uStepper/uStepperS/Examples/DropIn/DropIn.ino

/*
*			DropIn example sketch!
*
*		This sketch is all the software that is needed for adding closed loop position control 
*		To existing 3d printer controllers. 
*		
*		All of the PID parameters and current settings can be configured from the serial monitor (baud rate: 9600)
*		After this sketch has been uploaded, and the configured settings will be saved to EEPROM, so they are
*		persistent between powercycles.
*
*		The easiest way to connect it uStepper to the external controller, is to use a 3D shield on the uStepper
*		and a stepstick shield on the external controller 
*		(https://ustepper.com/store/shields/31-59-3d-shield.html#/38-3dshield-3d_shield_stepstick_right)
*		however this is only possible if the external controller normally uses step sticks. if this is not the case,
*		then the connections should be as follows:
*		
*
*	Pin connections:
*	-----------------------------
*	| Controller | uStepper S    |
*	|----------------------------|
*	|	Enable   |		D2		 |
*	|	Step     |		D3		 |
*	|	Dir      |		D4		 |
*	|	GND      |		GND		 |
*	------------------------------	
*
*
*		ATTENTION: There is a 10 second delay from powering up uStepper to accepting input - this is to avoid movement on control jitter when CNC/Printer board starts up !
*
*/
/********************************************************************************************
* 	    	File:  LimitDetection.ino                                                         *
*		Version:    2.3.0                                          						    *
*      	Date: 		December 27th, 2021  	                                    			*
*       Author:  Thomas Hørring Olsen                                                       *
*  Description:  DropIn example sketch!                                                     *
*                                                                                           *
*	This sketch is all the software that is needed for adding closed loop position control    *
*	To existing 3d printer controllers.                                                       *
*                                                                                           *
*	All of the PID parameters and current settings can be configured from the serial monitor  *
* (baud rate: 9600)                                                                         *
*	After this sketch has been uploaded, and the configured settings will be saved to EEPROM, *
* so they are persistent between powercycles.                                               *
*                                                                                           *
*	The easiest way to connect it uStepper to the external controller, is to use a 3D shield  *
* on the uStepper and a stepstick shield on the external controller                         * 
*	(https://ustepper.com/store/shields/31-59-3d-shield.html#/38-3dshield-3d_shield_stepstick_right)
*	however this is only possible if the external controller normally uses step sticks.       *
* If this is not the case, then the connections should be as follows:                       *
*                                                                                           *
*	Pin connections:                                                                          *
*	------------------------------                                                            *             
*	| Controller | uStepper S    |                                                            *
*	|----------------------------|                                                            *
*	|	Enable     |		D2		     |                                                            *
*	|	Step       |		D3		     |                                                            *
*	|	Dir        |		D4		     |                                                            *
*	|	GND        |		GND		     |                                                            *
*	------------------------------	                                                          *
*                                                                                           *
*                                                                                           *
*		ATTENTION: There is a 10 second delay from powering up uStepper to accepting input      *
*        - this is to avoid movement on control jitter when CNC/Printer board starts up !   *
*                                                                                           *
* For more information, check out the documentation:                                        * 
*                http://ustepper.com/docs/usteppers/html/index.html                         *
*                                                                                           *
*********************************************************************************************
*	(C) 2020                                                                                  *
*                                                                                           *
*	uStepper ApS                                                                              *
*	www.ustepper.com                                                                          *
*	administration@ustepper.com                                                               *
*                                                                                           *
*	The code contained in this file is released under the following open source license:      *
*                                                                                           *
*			Creative Commons Attribution-NonCommercial-ShareAlike 4.0 International               *
*                                                                                           *
* 	The code in this file is provided without warranty of any kind - use at own risk!       *
* 	neither uStepper ApS nor the author, can be held responsible for any damage             *
* 	caused by the use of the code contained in this file !                                  *
*                                                                                           *
*                                                                                           *
********************************************************************************************/

#include <uStepperS.h>
uStepperS stepper;

void setup() {

  Serial.begin(9600);
  stepper.setup(DROPIN, 200, 75, 7.0, 1.0);				// Dropin mode, 
  														// 200 fullsteps per revolution,
  														// P = 75
  														// I = 7
  														// D = 1
  stepper.checkOrientation(30.0);       				//Check orientation of motor connector with +/- 30 microsteps movement
}

void loop() {
  stepper.dropinCli();			// activate CLI interface to set parameters, current etc.
}
